ItsBreadTime/van-child-safety/test_runs/lab-validation/T-BLE-FP-ACTIVE-01/README.md

# T-BLE-FP-ACTIVE-01

Environment: simulated
Date/time: 2026-07-04T00:51:16+07:00
Firmware commit: 4d69e42
Ignition source: 
Relevant config: automated Bread iBeacon toggle while ignition_on active; verify no distress and bounded beacon chatter
Round count planned: 6
Operator: 
Supervisor: 

Physical setup:
- Door/window state:
- Fan/AC state:
- Sensor placement:
- Beacon placement:
- LD2412 target position:

Safety notes:
- Abort criteria:
- Actual abort condition reached: yes/no

Automation notes:
- MQTT log: `mqtt.log`
- Serial log: `serial.log`
- Relay snapshots: `relay_before.jsonl`, `relay_after.jsonl`
- Measurements: `measurements.csv`, `co2.csv`, `rssi.csv`
