ItsBreadTime/van-child-safety/test_runs/lab-validation/T-DISARM-02-LATENCY/README.md

# T-DISARM-02-LATENCY

Environment: simulated
Date/time: 2026-07-03T23:56:55+07:00
Firmware commit: 4d69e42
Ignition source: 
Relevant config: 10-round invalid disarm command-result latency measurement while bus is active
Round count planned: 10
Operator: 
Supervisor: 

Physical setup:
- Door/window state:
- Fan/AC state:
- Sensor placement:
- Beacon placement:
- LD2412 target position:

Safety notes:
- Abort criteria:
- Actual abort condition reached: yes/no

Automation notes:
- MQTT log: `mqtt.log`
- Serial log: `serial.log`
- Relay snapshots: `relay_before.jsonl`, `relay_after.jsonl`
- Measurements: `measurements.csv`, `co2.csv`, `rssi.csv`
