ItsBreadTime/van-child-safety/test_runs/lab-validation/T-DISARM-02/README.md

# T-DISARM-02

Environment: simulated
Date/time: 2026-07-03T23:42:01+07:00
Firmware commit: 4d69e42
Ignition source: 
Relevant config: invalid disarm without cabin-clear confirmation while bus is active
Round count planned: 3
Operator: 
Supervisor: 

Physical setup:
- Door/window state:
- Fan/AC state:
- Sensor placement:
- Beacon placement:
- LD2412 target position:

Safety notes:
- Abort criteria:
- Actual abort condition reached: yes/no

Automation notes:
- MQTT log: `mqtt.log`
- Serial log: `serial.log`
- Relay snapshots: `relay_before.jsonl`, `relay_after.jsonl`
- Measurements: `measurements.csv`, `co2.csv`, `rssi.csv`
