ItsBreadTime/van-child-safety/test_runs/lab-validation/T-HA-IGN-01/README.md

# T-HA-IGN-01

Environment: simulated-mqtt
Date/time: 2026-07-04T19:16:59+07:00
Firmware commit: 4d69e42
Ignition source: 
Relevant config: bus_empty_on/off override; observe MQTT bus/state fields consumed by HA entities
Round count planned: 1
Operator: operator
Supervisor: 

Physical setup:
- Door/window state:
- Fan/AC state:
- Sensor placement:
- Beacon placement:
- LD2412 target position:

Safety notes:
- Abort criteria:
- Actual abort condition reached: yes/no

Automation notes:
- MQTT log: `mqtt.log`
- Serial log: `serial.log`
- Relay snapshots: `relay_before.jsonl`, `relay_after.jsonl`
- Measurements: `measurements.csv`, `co2.csv`, `rssi.csv`
