ItsBreadTime/van-child-safety/test_runs/lab-validation/T-HA-ZONE-01/README.md

# T-HA-ZONE-01

Environment: simulated
Date/time: 2026-07-03T23:32:32+07:00
Firmware commit: 4d69e42
Ignition source: 
Relevant config: publish bus/ha/location/event zone_enter/zone_leave
Round count planned: 3
Operator: 
Supervisor: 

Physical setup:
- Door/window state:
- Fan/AC state:
- Sensor placement:
- Beacon placement:
- LD2412 target position:

Safety notes:
- Abort criteria:
- Actual abort condition reached: yes/no

Automation notes:
- MQTT log: `mqtt.log`
- Serial log: `serial.log`
- Relay snapshots: `relay_before.jsonl`, `relay_after.jsonl`
- Measurements: `measurements.csv`, `co2.csv`, `rssi.csv`
