ItsBreadTime/van-child-safety/test_runs/lab-validation/T-IGN-ESPNOW-01/README.md

# T-IGN-ESPNOW-01

Environment: simulated
Date/time: 2026-07-04T00:00:21+07:00
Firmware commit: 4d69e42
Ignition source: espnow
Relevant config: ESP-NOW remote unplug while active; observe ok to stale and active to exit_grace, then replug before armed distress
Round count planned: 1
Operator: 
Supervisor: 

Physical setup:
- Door/window state:
- Fan/AC state:
- Sensor placement:
- Beacon placement:
- LD2412 target position:

Safety notes:
- Abort criteria:
- Actual abort condition reached: yes/no

Automation notes:
- MQTT log: `mqtt.log`
- Serial log: `serial.log`
- Relay snapshots: `relay_before.jsonl`, `relay_after.jsonl`
- Measurements: `measurements.csv`, `co2.csv`, `rssi.csv`
