ItsBreadTime/van-child-safety/test_runs/lab-validation/T-LD-ARMENTRY-01/README.md

# T-LD-ARMENTRY-01

Environment: simulated
Date/time: 2026-07-04T13:14:01+07:00
Firmware commit: 4d69e42
Ignition source: 
Relevant config: desk proxy LD2412/mmWave armed trigger with target already present at arm time; real Discord distress allowed; fallback because passive target did not clear
Round count planned: 1
Operator: 
Supervisor: 

Physical setup:
- Door/window state:
- Fan/AC state:
- Sensor placement:
- Beacon placement:
- LD2412 target position:

Safety notes:
- Abort criteria:
- Actual abort condition reached: yes/no

Automation notes:
- MQTT log: `mqtt.log`
- Serial log: `serial.log`
- Relay snapshots: `relay_before.jsonl`, `relay_after.jsonl`
- Measurements: `measurements.csv`, `co2.csv`, `rssi.csv`
