ItsBreadTime/van-child-safety/test_runs/lab-validation/T-LD2412-PASSIVE-01/README.md

# T-LD2412-PASSIVE-01

Environment: simulated
Date/time: 2026-07-04T13:09:19+07:00
Firmware commit: 4d69e42
Ignition source: 
Relevant config: active-state LD2412/mmWave target movement observation; user moves out of and back into sensor range; no arming
Round count planned: 1
Operator: 
Supervisor: 

Physical setup:
- Door/window state:
- Fan/AC state:
- Sensor placement:
- Beacon placement:
- LD2412 target position:

Safety notes:
- Abort criteria:
- Actual abort condition reached: yes/no

Automation notes:
- MQTT log: `mqtt.log`
- Serial log: `serial.log`
- Relay snapshots: `relay_before.jsonl`, `relay_after.jsonl`
- Measurements: `measurements.csv`, `co2.csv`, `rssi.csv`
