ItsBreadTime/van-child-safety/test_runs/lab-validation/T-BLE-01/bread_beacon_test_logcat.txt

--------- beginning of system
07-04 12:09:19.528 <pid> <pid> I ActivityManager: Force stopping com.example.redacted appid=<id> user=<id>: from process=<id>
07-04 12:09:19.542 <pid> <pid> W ActivityManager: Invalid packageName: com.example.redacted
07-04 12:09:19.646 <pid> <pid> I ActivityManager: Start proc <pid>:<process> for next-top-activity {io.example.busbeacontest} caller=com.example.redacted
07-04 12:09:19.647 <pid> <pid> I ActivityManager: ProcessObserver broadcast disabled
--------- beginning of main
07-04 12:09:19.733 <pid> <pid> I BreadBeaconTest: command_activity action=io.example.busbeacontest
07-04 12:09:19.753 <pid> <pid> I ActivityManager: Background started FGS: Allowed [callingPackage: io.example.busbeacontest; callingUid=<id>; uidState: TOP ; uidBFSL: [BFSL]; intent: Intent { act=io.example.busbeacontest xflg=0x4 cmp=io.example.busbeacontest }; code:PROC_STATE_TOP; tempAllowListReason:<null>; allowWiu:12; targetSdkVersion=<version>; callerTargetSdkVersion=<version>; startForegroundCount=<count>; bindFromPackage:null: isBindService:false]
07-04 12:09:19.754 <pid> <pid> I ActivityManager: Cancel FGS notification userId=<id> definingUid=<id> packageName: io.example.busbeacontest processName:io.example.busbeacontest ChannelId:bread-beacon-test foregroundNotiWhen=<timestamp> Notiflags=<flags>
07-04 12:09:19.756 <pid> <pid> I ActivityManager: Cancel FGS notification userId=<id> definingUid=<id> packageName: io.example.busbeacontest processName:io.example.busbeacontest ChannelId:bread-beacon-test foregroundNotiWhen=<timestamp> Notiflags=<flags>
07-04 12:09:21.856 <pid> <pid> I BreadBeaconTest: command_activity action=io.example.busbeacontest
07-04 12:09:21.857 <pid> <pid> I ActivityManager: Background started FGS: Allowed [callingPackage: io.example.busbeacontest; callingUid=<id>; uidState: TOP ; uidBFSL: [BFSL]; intent: Intent { act=io.example.busbeacontest xflg=0x4 cmp=io.example.busbeacontest }; code:PROC_STATE_TOP; tempAllowListReason:<null>; allowWiu:12; targetSdkVersion=<version>; callerTargetSdkVersion=<version>; startForegroundCount=<count>; bindFromPackage:null: isBindService:false]
07-04 12:09:21.870 <pid> <pid> D BluetoothLeAdvertiser: TxPower == ADVERTISE_TX_POWER_HIGH
07-04 12:09:21.873 <pid> <pid> I BreadBeaconTest: advertise_start_requested uuid=00000000-0000-4000-8000-000000000000 major=1001 minor=2001
07-04 12:09:21.889 <pid> <pid> I BreadBeaconTest: advertise_start_success
07-04 12:09:23.995 <pid> <pid> I ActivityManager: Start proc <pid>:<process> for broadcast {com.example.redacted} caller=com.example.redacted
07-04 12:09:23.995 <pid> <pid> I ActivityManager: ProcessObserver broadcast disabled
07-04 12:09:24.772 <pid> <pid> I ActivityManager: unbindService com.example.redacted@<object> conn=android.os.BinderProxy@<object> callingPid=<id>
07-04 12:09:24.774 <pid> <pid> I ActivityManager: unbindService com.example.redacted@<object> conn=android.os.BinderProxy@<object> callingPid=<id>
07-04 12:09:24.779 <pid> <pid> I ActivityManager: unbindService com.example.redacted@<object> conn=android.os.BinderProxy@<object> callingPid=<id>
07-04 12:09:24.798 <pid> <pid> I ActivityManager: unbindService com.example.redacted@<object> conn=android.os.BinderProxy@<object> callingPid=<id>
07-04 12:09:24.815 <pid> <pid> I ActivityManager: unbindService com.example.redacted@<object> conn=android.os.BinderProxy@<object> callingPid=<id>
07-04 12:09:24.875 <pid> <pid> I ActivityManager: Killing <pid>:<process> (adj 905): normal_mem_pressure
07-04 12:09:25.165 <pid> <pid> I ActivityManager: unbindService com.example.redacted@<object> conn=android.os.BinderProxy@<object> callingPid=<id>
07-04 12:09:25.234 <pid> <pid> I ActivityManager: unbindService com.example.redacted@<object> conn=android.os.BinderProxy@<object> callingPid=<id>
07-04 12:09:25.434 <pid> <pid> I ActivityManager: Start proc <pid>:<process> for content provider {com.example.redacted} caller=com.example.redacted
07-04 12:09:25.435 <pid> <pid> I ActivityManager: ProcessObserver broadcast disabled
07-04 12:09:25.895 <pid> <pid> W ActivityManager: pid=<id> com.example.redacted sent binder code 1 with flags 2 to frozen apps and got error -74
07-04 12:09:25.903 <pid> <pid> W ActivityManager: pid=<id> com.example.redacted sent binder code 1 with flags 2 to frozen apps and got error -74
07-04 12:09:26.529 <pid> <pid> W ActivityManager: Unbind failed: could not find connection for android.os.BinderProxy@<object>
07-04 12:09:26.530 <pid> <pid> W ActivityManager: Unable to start service Intent { act=android.telephony.satellite.SatelliteService xflg=0x4 pkg=com.example.redacted } U=0: not found
07-04 12:09:32.531 <pid> <pid> I ActivityManager: unbindService com.example.redacted@<object> conn=android.os.BinderProxy@<object> callingPid=<id>
07-04 12:09:33.549 <pid> <pid> I ActivityManager: unbindService com.example.redacted@<object> conn=android.os.BinderProxy@<object> callingPid=<id>
07-04 12:09:39.002 <pid> <pid> I ActivityManager: unbindService com.example.redacted@<object> conn=android.os.BinderProxy@<object> callingPid=<id>
07-04 12:09:39.787 <pid> <pid> I ActivityManager: unbindService com.example.redacted@<object> conn=android.os.BinderProxy@<object> callingPid=<id>
07-04 12:09:39.789 <pid> <pid> I ActivityManager: unbindService com.example.redacted@<object> conn=android.os.BinderProxy@<object> callingPid=<id>
07-04 12:09:40.200 <pid> <pid> I ActivityManager: unbindService com.example.redacted@<object> conn=android.os.BinderProxy@<object> callingPid=<id>
07-04 12:09:40.207 <pid> <pid> I ActivityManager: unbindService com.example.redacted@<object> conn=android.os.BinderProxy@<object> callingPid=<id>
07-04 12:09:40.325 <pid> <pid> I ActivityManager: Start proc <pid>:<process> for service {com.example.redacted} caller=com.example.redacted
07-04 12:09:40.325 <pid> <pid> I ActivityManager: ProcessObserver broadcast disabled
07-04 12:09:41.819 <pid> <pid> I ActivityManager: unbindService com.example.redacted@<object> conn=android.app.LoadedApk$ServiceDispatcher$InnerConnection@<object> callingPid=<id> callers: com.example.redacted:5455 com.example.redacted:5328 com.example.redacted:5626 com.example.redacted:3471 android.accounts.IAccountAuthenticatorResponse$Stub.onTransact:106 android.os.Binder.execTransactInternal:1433 android.os.Binder.execTransact:1372 <bottom of call stack> <bottom of call stack> <bottom of call stack> 
07-04 12:09:43.334 <pid> <pid> I ActivityManager: unbindService com.example.redacted@<object> conn=android.app.LoadedApk$ServiceDispatcher$InnerConnection@<object> callingPid=<id> callers: com.example.redacted:5455 com.example.redacted:5328 com.example.redacted:5626 com.example.redacted:3471 android.accounts.IAccountAuthenticatorResponse$Stub.onTransact:106 android.os.Binder.execTransactInternal:1433 android.os.Binder.execTransact:1372 <bottom of call stack> <bottom of call stack> <bottom of call stack> 
07-04 12:09:44.851 <pid> <pid> I ActivityManager: unbindService com.example.redacted@<object> conn=android.app.LoadedApk$ServiceDispatcher$InnerConnection@<object> callingPid=<id> callers: com.example.redacted:5455 com.example.redacted:5328 com.example.redacted:5626 com.example.redacted:3471 android.accounts.IAccountAuthenticatorResponse$Stub.onTransact:106 android.os.Binder.execTransactInternal:1433 android.os.Binder.execTransact:1372 <bottom of call stack> <bottom of call stack> <bottom of call stack> 
07-04 12:09:46.364 <pid> <pid> I ActivityManager: unbindService com.example.redacted@<object> conn=android.app.LoadedApk$ServiceDispatcher$InnerConnection@<object> callingPid=<id> callers: com.example.redacted:5455 com.example.redacted:5328 com.example.redacted:5626 com.example.redacted:3471 android.accounts.IAccountAuthenticatorResponse$Stub.onTransact:106 android.os.Binder.execTransactInternal:1433 android.os.Binder.execTransact:1372 <bottom of call stack> <bottom of call stack> <bottom of call stack> 
07-04 12:09:46.518 <pid> <pid> I ActivityManager: Waited long enough for: ServiceRecord{5984d0c u0 com.example.redacted c:com.example.redacted}
07-04 12:09:47.876 <pid> <pid> I ActivityManager: unbindService com.example.redacted@<object> conn=android.app.LoadedApk$ServiceDispatcher$InnerConnection@<object> callingPid=<id> callers: com.example.redacted:5455 com.example.redacted:5328 com.example.redacted:5626 com.example.redacted:3471 android.accounts.IAccountAuthenticatorResponse$Stub.onTransact:106 android.os.Binder.execTransactInternal:1433 android.os.Binder.execTransact:1372 <bottom of call stack> <bottom of call stack> <bottom of call stack> 
07-04 12:09:49.022 <pid> <pid> I ActivityManager: unbindService com.example.redacted@<object> conn=android.os.BinderProxy@<object> callingPid=<id>
07-04 12:09:49.391 <pid> <pid> I ActivityManager: unbindService com.example.redacted@<object> conn=android.app.LoadedApk$ServiceDispatcher$InnerConnection@<object> callingPid=<id> callers: com.example.redacted:5455 com.example.redacted:5328 com.example.redacted:5626 com.example.redacted:3471 android.accounts.IAccountAuthenticatorResponse$Stub.onTransact:106 android.os.Binder.execTransactInternal:1433 android.os.Binder.execTransact:1372 <bottom of call stack> <bottom of call stack> <bottom of call stack> 
07-04 12:09:50.550 <pid> <pid> W ActivityManager: Unable to start service Intent { act=onetrack.action.TRACK_EVENT flg=0x2 xflg=0x4 pkg=com.example.redacted (has extras) } U=0: not found
07-04 12:09:50.906 <pid> <pid> I ActivityManager: unbindService com.example.redacted@<object> conn=android.app.LoadedApk$ServiceDispatcher$InnerConnection@<object> callingPid=<id> callers: com.example.redacted:5455 com.example.redacted:5328 com.example.redacted:5626 com.example.redacted:3471 android.accounts.IAccountAuthenticatorResponse$Stub.onTransact:106 android.os.Binder.execTransactInternal:1433 android.os.Binder.execTransact:1372 <bottom of call stack> <bottom of call stack> <bottom of call stack> 
07-04 12:09:52.421 <pid> <pid> I ActivityManager: unbindService com.example.redacted@<object> conn=android.app.LoadedApk$ServiceDispatcher$InnerConnection@<object> callingPid=<id> callers: com.example.redacted:5455 com.example.redacted:5328 com.example.redacted:5626 com.example.redacted:3471 android.accounts.IAccountAuthenticatorResponse$Stub.onTransact:106 android.os.Binder.execTransactInternal:1433 android.os.Binder.execTransact:1372 <bottom of call stack> <bottom of call stack> <bottom of call stack> 
07-04 12:09:53.937 <pid> <pid> I ActivityManager: unbindService com.example.redacted@<object> conn=android.app.LoadedApk$ServiceDispatcher$InnerConnection@<object> callingPid=<id> callers: com.example.redacted:5455 com.example.redacted:5328 com.example.redacted:5626 com.example.redacted:3471 android.accounts.IAccountAuthenticatorResponse$Stub.onTransact:106 android.os.Binder.execTransactInternal:1433 android.os.Binder.execTransact:1372 <bottom of call stack> <bottom of call stack> <bottom of call stack> 
07-04 12:09:54.707 <pid> <pid> I ActivityManager: unbindService com.example.redacted@<object> conn=android.os.BinderProxy@<object> callingPid=<id>
07-04 12:09:55.451 <pid> <pid> I ActivityManager: unbindService com.example.redacted@<object> conn=android.app.LoadedApk$ServiceDispatcher$InnerConnection@<object> callingPid=<id> callers: com.example.redacted:5455 com.example.redacted:5328 com.example.redacted:5626 com.example.redacted:3471 android.accounts.IAccountAuthenticatorResponse$Stub.onTransact:106 android.os.Binder.execTransactInternal:1433 android.os.Binder.execTransact:1372 <bottom of call stack> <bottom of call stack> <bottom of call stack> 
07-04 12:09:56.969 <pid> <pid> I ActivityManager: unbindService com.example.redacted@<object> conn=android.app.LoadedApk$ServiceDispatcher$InnerConnection@<object> callingPid=<id> callers: com.example.redacted:5455 com.example.redacted:5328 com.example.redacted:5626 com.example.redacted:3471 android.accounts.IAccountAuthenticatorResponse$Stub.onTransact:106 android.os.Binder.execTransactInternal:1433 android.os.Binder.execTransact:1372 <bottom of call stack> <bottom of call stack> <bottom of call stack> 
07-04 12:09:58.163 <pid> <pid> W ActivityManager: Unable to start service Intent { xflg=0x4 cmp=com.example.redacted } U=0: not found
07-04 12:09:58.483 <pid> <pid> I ActivityManager: unbindService com.example.redacted@<object> conn=android.app.LoadedApk$ServiceDispatcher$InnerConnection@<object> callingPid=<id> callers: com.example.redacted:5455 com.example.redacted:5328 com.example.redacted:5626 com.example.redacted:3471 android.accounts.IAccountAuthenticatorResponse$Stub.onTransact:106 android.os.Binder.execTransactInternal:1433 android.os.Binder.execTransact:1372 <bottom of call stack> <bottom of call stack> <bottom of call stack> 
07-04 12:09:59.998 <pid> <pid> I ActivityManager: unbindService com.example.redacted@<object> conn=android.app.LoadedApk$ServiceDispatcher$InnerConnection@<object> callingPid=<id> callers: com.example.redacted:5455 com.example.redacted:5328 com.example.redacted:5626 com.example.redacted:3471 android.accounts.IAccountAuthenticatorResponse$Stub.onTransact:106 android.os.Binder.execTransactInternal:1433 android.os.Binder.execTransact:1372 <bottom of call stack> <bottom of call stack> <bottom of call stack> 
07-04 12:10:00.809 <pid> <pid> W ActivityManager: Unbind failed: could not find connection for android.os.BinderProxy@<object>
07-04 12:10:00.811 <pid> <pid> W ActivityManager: Unable to start service Intent { act=android.telephony.satellite.SatelliteService xflg=0x4 pkg=com.example.redacted } U=0: not found
07-04 12:10:01.519 <pid> <pid> I ActivityManager: unbindService com.example.redacted@<object> conn=android.app.LoadedApk$ServiceDispatcher$InnerConnection@<object> callingPid=<id> callers: com.example.redacted:5455 com.example.redacted:5328 com.example.redacted:5626 com.example.redacted:3471 android.accounts.IAccountAuthenticatorResponse$Stub.onTransact:106 android.os.Binder.execTransactInternal:1433 android.os.Binder.execTransact:1372 <bottom of call stack> <bottom of call stack> <bottom of call stack> 
07-04 12:10:03.034 <pid> <pid> I ActivityManager: unbindService com.example.redacted@<object> conn=android.app.LoadedApk$ServiceDispatcher$InnerConnection@<object> callingPid=<id> callers: com.example.redacted:5455 com.example.redacted:5328 com.example.redacted:5626 com.example.redacted:3471 android.accounts.IAccountAuthenticatorResponse$Stub.onTransact:106 android.os.Binder.execTransactInternal:1433 android.os.Binder.execTransact:1372 <bottom of call stack> <bottom of call stack> <bottom of call stack> 
07-04 12:10:04.553 <pid> <pid> I ActivityManager: unbindService com.example.redacted@<object> conn=android.app.LoadedApk$ServiceDispatcher$InnerConnection@<object> callingPid=<id> callers: com.example.redacted:5455 com.example.redacted:5328 com.example.redacted:5626 com.example.redacted:3471 android.accounts.IAccountAuthenticatorResponse$Stub.onTransact:106 android.os.Binder.execTransactInternal:1433 android.os.Binder.execTransact:1372 <bottom of call stack> <bottom of call stack> <bottom of call stack> 
07-04 12:10:06.069 <pid> <pid> I ActivityManager: unbindService com.example.redacted@<object> conn=android.app.LoadedApk$ServiceDispatcher$InnerConnection@<object> callingPid=<id> callers: com.example.redacted:5455 com.example.redacted:5328 com.example.redacted:5626 com.example.redacted:3471 android.accounts.IAccountAuthenticatorResponse$Stub.onTransact:106 android.os.Binder.execTransactInternal:1433 android.os.Binder.execTransact:1372 <bottom of call stack> <bottom of call stack> <bottom of call stack> 
07-04 12:10:07.588 <pid> <pid> I ActivityManager: unbindService com.example.redacted@<object> conn=android.app.LoadedApk$ServiceDispatcher$InnerConnection@<object> callingPid=<id> callers: com.example.redacted:5455 com.example.redacted:5328 com.example.redacted:5626 com.example.redacted:3471 android.accounts.IAccountAuthenticatorResponse$Stub.onTransact:106 android.os.Binder.execTransactInternal:1433 android.os.Binder.execTransact:1372 <bottom of call stack> <bottom of call stack> <bottom of call stack> 
07-04 12:10:09.108 <pid> <pid> I ActivityManager: unbindService com.example.redacted@<object> conn=android.app.LoadedApk$ServiceDispatcher$InnerConnection@<object> callingPid=<id> callers: com.example.redacted:5455 com.example.redacted:5328 com.example.redacted:5626 com.example.redacted:3471 android.accounts.IAccountAuthenticatorResponse$Stub.onTransact:106 android.os.Binder.execTransactInternal:1433 android.os.Binder.execTransact:1372 <bottom of call stack> <bottom of call stack> <bottom of call stack> 
07-04 12:10:09.694 <pid> <pid> I ActivityManager: unbindService com.example.redacted@<object> conn=android.os.BinderProxy@<object> callingPid=<id>
07-04 12:10:10.626 <pid> <pid> I ActivityManager: unbindService com.example.redacted@<object> conn=android.app.LoadedApk$ServiceDispatcher$InnerConnection@<object> callingPid=<id> callers: com.example.redacted:5455 com.example.redacted:5328 com.example.redacted:5626 com.example.redacted:3471 android.accounts.IAccountAuthenticatorResponse$Stub.onTransact:106 android.os.Binder.execTransactInternal:1433 android.os.Binder.execTransact:1372 <bottom of call stack> <bottom of call stack> <bottom of call stack> 
07-04 12:10:12.143 <pid> <pid> I ActivityManager: unbindService com.example.redacted@<object> conn=android.app.LoadedApk$ServiceDispatcher$InnerConnection@<object> callingPid=<id> callers: com.example.redacted:5455 com.example.redacted:5328 com.example.redacted:5626 com.example.redacted:3471 android.accounts.IAccountAuthenticatorResponse$Stub.onTransact:106 android.os.Binder.execTransactInternal:1433 android.os.Binder.execTransact:1372 <bottom of call stack> <bottom of call stack> <bottom of call stack> 
07-04 12:10:13.662 <pid> <pid> I ActivityManager: unbindService com.example.redacted@<object> conn=android.app.LoadedApk$ServiceDispatcher$InnerConnection@<object> callingPid=<id> callers: com.example.redacted:5455 com.example.redacted:5328 com.example.redacted:5626 com.example.redacted:3471 android.accounts.IAccountAuthenticatorResponse$Stub.onTransact:106 android.os.Binder.execTransactInternal:1433 android.os.Binder.execTransact:1372 <bottom of call stack> <bottom of call stack> <bottom of call stack> 
07-04 12:10:15.175 <pid> <pid> I ActivityManager: unbindService com.example.redacted@<object> conn=android.app.LoadedApk$ServiceDispatcher$InnerConnection@<object> callingPid=<id> callers: com.example.redacted:5455 com.example.redacted:5328 com.example.redacted:5626 com.example.redacted:3471 android.accounts.IAccountAuthenticatorResponse$Stub.onTransact:106 android.os.Binder.execTransactInternal:1433 android.os.Binder.execTransact:1372 <bottom of call stack> <bottom of call stack> <bottom of call stack> 
07-04 12:10:16.692 <pid> <pid> I ActivityManager: unbindService com.example.redacted@<object> conn=android.app.LoadedApk$ServiceDispatcher$InnerConnection@<object> callingPid=<id> callers: com.example.redacted:5455 com.example.redacted:5328 com.example.redacted:5626 com.example.redacted:3471 android.accounts.IAccountAuthenticatorResponse$Stub.onTransact:106 android.os.Binder.execTransactInternal:1433 android.os.Binder.execTransact:1372 <bottom of call stack> <bottom of call stack> <bottom of call stack> 
07-04 12:10:18.208 <pid> <pid> I ActivityManager: unbindService com.example.redacted@<object> conn=android.app.LoadedApk$ServiceDispatcher$InnerConnection@<object> callingPid=<id> callers: com.example.redacted:5455 com.example.redacted:5328 com.example.redacted:5626 com.example.redacted:3471 android.accounts.IAccountAuthenticatorResponse$Stub.onTransact:106 android.os.Binder.execTransactInternal:1433 android.os.Binder.execTransact:1372 <bottom of call stack> <bottom of call stack> <bottom of call stack> 
07-04 12:10:19.726 <pid> <pid> I ActivityManager: unbindService com.example.redacted@<object> conn=android.app.LoadedApk$ServiceDispatcher$InnerConnection@<object> callingPid=<id> callers: com.example.redacted:5455 com.example.redacted:5328 com.example.redacted:5626 com.example.redacted:3471 android.accounts.IAccountAuthenticatorResponse$Stub.onTransact:106 android.os.Binder.execTransactInternal:1433 android.os.Binder.execTransact:1372 <bottom of call stack> <bottom of call stack> <bottom of call stack> 
07-04 12:10:21.242 <pid> <pid> I ActivityManager: unbindService com.example.redacted@<object> conn=android.app.LoadedApk$ServiceDispatcher$InnerConnection@<object> callingPid=<id> callers: com.example.redacted:5455 com.example.redacted:5328 com.example.redacted:5626 com.example.redacted:3471 android.accounts.IAccountAuthenticatorResponse$Stub.onTransact:106 android.os.Binder.execTransactInternal:1433 android.os.Binder.execTransact:1372 <bottom of call stack> <bottom of call stack> <bottom of call stack> 
07-04 12:10:22.756 <pid> <pid> I ActivityManager: unbindService com.example.redacted@<object> conn=android.app.LoadedApk$ServiceDispatcher$InnerConnection@<object> callingPid=<id> callers: com.example.redacted:5455 com.example.redacted:5328 com.example.redacted:5626 com.example.redacted:3471 android.accounts.IAccountAuthenticatorResponse$Stub.onTransact:106 android.os.Binder.execTransactInternal:1433 android.os.Binder.execTransact:1372 <bottom of call stack> <bottom of call stack> <bottom of call stack> 
07-04 12:10:24.273 <pid> <pid> I ActivityManager: unbindService com.example.redacted@<object> conn=android.app.LoadedApk$ServiceDispatcher$InnerConnection@<object> callingPid=<id> callers: com.example.redacted:5455 com.example.redacted:5328 com.example.redacted:5626 com.example.redacted:3471 android.accounts.IAccountAuthenticatorResponse$Stub.onTransact:106 android.os.Binder.execTransactInternal:1433 android.os.Binder.execTransact:1372 <bottom of call stack> <bottom of call stack> <bottom of call stack> 
07-04 12:10:25.790 <pid> <pid> I ActivityManager: unbindService com.example.redacted@<object> conn=android.app.LoadedApk$ServiceDispatcher$InnerConnection@<object> callingPid=<id> callers: com.example.redacted:5455 com.example.redacted:5328 com.example.redacted:5626 com.example.redacted:3471 android.accounts.IAccountAuthenticatorResponse$Stub.onTransact:106 android.os.Binder.execTransactInternal:1433 android.os.Binder.execTransact:1372 <bottom of call stack> <bottom of call stack> <bottom of call stack> 
07-04 12:10:27.307 <pid> <pid> I ActivityManager: unbindService com.example.redacted@<object> conn=android.app.LoadedApk$ServiceDispatcher$InnerConnection@<object> callingPid=<id> callers: com.example.redacted:5455 com.example.redacted:5328 com.example.redacted:5626 com.example.redacted:3471 android.accounts.IAccountAuthenticatorResponse$Stub.onTransact:106 android.os.Binder.execTransactInternal:1433 android.os.Binder.execTransact:1372 <bottom of call stack> <bottom of call stack> <bottom of call stack> 
07-04 12:10:28.822 <pid> <pid> I ActivityManager: unbindService com.example.redacted@<object> conn=android.app.LoadedApk$ServiceDispatcher$InnerConnection@<object> callingPid=<id> callers: com.example.redacted:5455 com.example.redacted:5328 com.example.redacted:5626 com.example.redacted:3471 android.accounts.IAccountAuthenticatorResponse$Stub.onTransact:106 android.os.Binder.execTransactInternal:1433 android.os.Binder.execTransact:1372 <bottom of call stack> <bottom of call stack> <bottom of call stack> 
07-04 12:10:30.342 <pid> <pid> I ActivityManager: unbindService com.example.redacted@<object> conn=android.app.LoadedApk$ServiceDispatcher$InnerConnection@<object> callingPid=<id> callers: com.example.redacted:5455 com.example.redacted:5328 com.example.redacted:5626 com.example.redacted:3471 android.accounts.IAccountAuthenticatorResponse$Stub.onTransact:106 android.os.Binder.execTransactInternal:1433 android.os.Binder.execTransact:1372 <bottom of call stack> <bottom of call stack> <bottom of call stack> 
07-04 12:10:31.853 <pid> <pid> I ActivityManager: unbindService com.example.redacted@<object> conn=android.app.LoadedApk$ServiceDispatcher$InnerConnection@<object> callingPid=<id> callers: com.example.redacted:5455 com.example.redacted:5328 com.example.redacted:5626 com.example.redacted:3471 android.accounts.IAccountAuthenticatorResponse$Stub.onTransact:106 android.os.Binder.execTransactInternal:1433 android.os.Binder.execTransact:1372 <bottom of call stack> <bottom of call stack> <bottom of call stack> 
07-04 12:10:33.364 <pid> <pid> I ActivityManager: unbindService com.example.redacted@<object> conn=android.app.LoadedApk$ServiceDispatcher$InnerConnection@<object> callingPid=<id> callers: com.example.redacted:5455 com.example.redacted:5328 com.example.redacted:5626 com.example.redacted:3471 android.accounts.IAccountAuthenticatorResponse$Stub.onTransact:106 android.os.Binder.execTransactInternal:1433 android.os.Binder.execTransact:1372 <bottom of call stack> <bottom of call stack> <bottom of call stack> 
07-04 12:10:34.875 <pid> <pid> I ActivityManager: unbindService com.example.redacted@<object> conn=android.app.LoadedApk$ServiceDispatcher$InnerConnection@<object> callingPid=<id> callers: com.example.redacted:5455 com.example.redacted:5328 com.example.redacted:5626 com.example.redacted:3471 android.accounts.IAccountAuthenticatorResponse$Stub.onTransact:106 android.os.Binder.execTransactInternal:1433 android.os.Binder.execTransact:1372 <bottom of call stack> <bottom of call stack> <bottom of call stack> 
07-04 12:10:36.394 <pid> <pid> I ActivityManager: unbindService com.example.redacted@<object> conn=android.app.LoadedApk$ServiceDispatcher$InnerConnection@<object> callingPid=<id> callers: com.example.redacted:5455 com.example.redacted:5328 com.example.redacted:5626 com.example.redacted:3471 android.accounts.IAccountAuthenticatorResponse$Stub.onTransact:106 android.os.Binder.execTransactInternal:1433 android.os.Binder.execTransact:1372 <bottom of call stack> <bottom of call stack> <bottom of call stack> 
07-04 12:10:37.913 <pid> <pid> I ActivityManager: unbindService com.example.redacted@<object> conn=android.app.LoadedApk$ServiceDispatcher$InnerConnection@<object> callingPid=<id> callers: com.example.redacted:5455 com.example.redacted:5328 com.example.redacted:5626 com.example.redacted:3471 android.accounts.IAccountAuthenticatorResponse$Stub.onTransact:106 android.os.Binder.execTransactInternal:1433 android.os.Binder.execTransact:1372 <bottom of call stack> <bottom of call stack> <bottom of call stack> 
07-04 12:10:39.427 <pid> <pid> I ActivityManager: unbindService com.example.redacted@<object> conn=android.app.LoadedApk$ServiceDispatcher$InnerConnection@<object> callingPid=<id> callers: com.example.redacted:5455 com.example.redacted:5328 com.example.redacted:5626 com.example.redacted:3471 android.accounts.IAccountAuthenticatorResponse$Stub.onTransact:106 android.os.Binder.execTransactInternal:1433 android.os.Binder.execTransact:1372 <bottom of call stack> <bottom of call stack> <bottom of call stack> 
07-04 12:10:40.942 <pid> <pid> I ActivityManager: unbindService com.example.redacted@<object> conn=android.app.LoadedApk$ServiceDispatcher$InnerConnection@<object> callingPid=<id> callers: com.example.redacted:5455 com.example.redacted:5328 com.example.redacted:5626 com.example.redacted:3471 android.accounts.IAccountAuthenticatorResponse$Stub.onTransact:106 android.os.Binder.execTransactInternal:1433 android.os.Binder.execTransact:1372 <bottom of call stack> <bottom of call stack> <bottom of call stack> 
07-04 12:10:42.461 <pid> <pid> I ActivityManager: unbindService com.example.redacted@<object> conn=android.app.LoadedApk$ServiceDispatcher$InnerConnection@<object> callingPid=<id> callers: com.example.redacted:5455 com.example.redacted:5328 com.example.redacted:5626 com.example.redacted:3471 android.accounts.IAccountAuthenticatorResponse$Stub.onTransact:106 android.os.Binder.execTransactInternal:1433 android.os.Binder.execTransact:1372 <bottom of call stack> <bottom of call stack> <bottom of call stack> 
07-04 12:10:43.974 <pid> <pid> I ActivityManager: unbindService com.example.redacted@<object> conn=android.app.LoadedApk$ServiceDispatcher$InnerConnection@<object> callingPid=<id> callers: com.example.redacted:5455 com.example.redacted:5328 com.example.redacted:5626 com.example.redacted:3471 android.accounts.IAccountAuthenticatorResponse$Stub.onTransact:106 android.os.Binder.execTransactInternal:1433 android.os.Binder.execTransact:1372 <bottom of call stack> <bottom of call stack> <bottom of call stack> 
07-04 12:10:44.374 <pid> <pid> W ActivityManager: Unbind failed: could not find connection for android.os.BinderProxy@<object>
07-04 12:10:44.376 <pid> <pid> W ActivityManager: Unable to start service Intent { act=android.telephony.satellite.SatelliteService xflg=0x4 pkg=com.example.redacted } U=0: not found
07-04 12:10:45.489 <pid> <pid> I ActivityManager: unbindService com.example.redacted@<object> conn=android.app.LoadedApk$ServiceDispatcher$InnerConnection@<object> callingPid=<id> callers: com.example.redacted:5455 com.example.redacted:5328 com.example.redacted:5626 com.example.redacted:3471 android.accounts.IAccountAuthenticatorResponse$Stub.onTransact:106 android.os.Binder.execTransactInternal:1433 android.os.Binder.execTransact:1372 <bottom of call stack> <bottom of call stack> <bottom of call stack> 
07-04 12:10:47.005 <pid> <pid> I ActivityManager: unbindService com.example.redacted@<object> conn=android.app.LoadedApk$ServiceDispatcher$InnerConnection@<object> callingPid=<id> callers: com.example.redacted:5455 com.example.redacted:5328 com.example.redacted:5626 com.example.redacted:3471 android.accounts.IAccountAuthenticatorResponse$Stub.onTransact:106 android.os.Binder.execTransactInternal:1433 android.os.Binder.execTransact:1372 <bottom of call stack> <bottom of call stack> <bottom of call stack> 
07-04 12:10:48.520 <pid> <pid> I ActivityManager: unbindService com.example.redacted@<object> conn=android.app.LoadedApk$ServiceDispatcher$InnerConnection@<object> callingPid=<id> callers: com.example.redacted:5455 com.example.redacted:5328 com.example.redacted:5626 com.example.redacted:3471 android.accounts.IAccountAuthenticatorResponse$Stub.onTransact:106 android.os.Binder.execTransactInternal:1433 android.os.Binder.execTransact:1372 <bottom of call stack> <bottom of call stack> <bottom of call stack> 
07-04 12:10:50.035 <pid> <pid> I ActivityManager: unbindService com.example.redacted@<object> conn=android.app.LoadedApk$ServiceDispatcher$InnerConnection@<object> callingPid=<id> callers: com.example.redacted:5455 com.example.redacted:5328 com.example.redacted:5626 com.example.redacted:3471 android.accounts.IAccountAuthenticatorResponse$Stub.onTransact:106 android.os.Binder.execTransactInternal:1433 android.os.Binder.execTransact:1372 <bottom of call stack> <bottom of call stack> <bottom of call stack> 
07-04 12:10:51.550 <pid> <pid> I ActivityManager: unbindService com.example.redacted@<object> conn=android.app.LoadedApk$ServiceDispatcher$InnerConnection@<object> callingPid=<id> callers: com.example.redacted:5455 com.example.redacted:5328 com.example.redacted:5626 com.example.redacted:3471 android.accounts.IAccountAuthenticatorResponse$Stub.onTransact:106 android.os.Binder.execTransactInternal:1433 android.os.Binder.execTransact:1372 <bottom of call stack> <bottom of call stack> <bottom of call stack> 
07-04 12:10:53.067 <pid> <pid> I ActivityManager: unbindService com.example.redacted@<object> conn=android.app.LoadedApk$ServiceDispatcher$InnerConnection@<object> callingPid=<id> callers: com.example.redacted:5455 com.example.redacted:5328 com.example.redacted:5626 com.example.redacted:3471 android.accounts.IAccountAuthenticatorResponse$Stub.onTransact:106 android.os.Binder.execTransactInternal:1433 android.os.Binder.execTransact:1372 <bottom of call stack> <bottom of call stack> <bottom of call stack> 
07-04 12:10:54.582 <pid> <pid> I ActivityManager: unbindService com.example.redacted@<object> conn=android.app.LoadedApk$ServiceDispatcher$InnerConnection@<object> callingPid=<id> callers: com.example.redacted:5455 com.example.redacted:5328 com.example.redacted:5626 com.example.redacted:3471 android.accounts.IAccountAuthenticatorResponse$Stub.onTransact:106 android.os.Binder.execTransactInternal:1433 android.os.Binder.execTransact:1372 <bottom of call stack> <bottom of call stack> <bottom of call stack> 
07-04 12:10:56.103 <pid> <pid> I ActivityManager: unbindService com.example.redacted@<object> conn=android.app.LoadedApk$ServiceDispatcher$InnerConnection@<object> callingPid=<id> callers: com.example.redacted:5455 com.example.redacted:5328 com.example.redacted:5626 com.example.redacted:3471 android.accounts.IAccountAuthenticatorResponse$Stub.onTransact:106 android.os.Binder.execTransactInternal:1433 android.os.Binder.execTransact:1372 <bottom of call stack> <bottom of call stack> <bottom of call stack> 
07-04 12:10:57.617 <pid> <pid> I ActivityManager: unbindService com.example.redacted@<object> conn=android.app.LoadedApk$ServiceDispatcher$InnerConnection@<object> callingPid=<id> callers: com.example.redacted:5455 com.example.redacted:5328 com.example.redacted:5626 com.example.redacted:3471 android.accounts.IAccountAuthenticatorResponse$Stub.onTransact:106 android.os.Binder.execTransactInternal:1433 android.os.Binder.execTransact:1372 <bottom of call stack> <bottom of call stack> <bottom of call stack> 
07-04 12:10:58.201 <pid> <pid> W ActivityManager: Unable to start service Intent { xflg=0x4 cmp=com.example.redacted } U=0: not found
07-04 12:10:59.130 <pid> <pid> I ActivityManager: unbindService com.example.redacted@<object> conn=android.app.LoadedApk$ServiceDispatcher$InnerConnection@<object> callingPid=<id> callers: com.example.redacted:5455 com.example.redacted:5328 com.example.redacted:5626 com.example.redacted:3471 android.accounts.IAccountAuthenticatorResponse$Stub.onTransact:106 android.os.Binder.execTransactInternal:1433 android.os.Binder.execTransact:1372 <bottom of call stack> <bottom of call stack> <bottom of call stack> 
07-04 12:11:00.643 <pid> <pid> I ActivityManager: unbindService com.example.redacted@<object> conn=android.app.LoadedApk$ServiceDispatcher$InnerConnection@<object> callingPid=<id> callers: com.example.redacted:5455 com.example.redacted:5328 com.example.redacted:5626 com.example.redacted:3471 android.accounts.IAccountAuthenticatorResponse$Stub.onTransact:106 android.os.Binder.execTransactInternal:1433 android.os.Binder.execTransact:1372 <bottom of call stack> <bottom of call stack> <bottom of call stack> 
07-04 12:11:02.159 <pid> <pid> I ActivityManager: unbindService com.example.redacted@<object> conn=android.app.LoadedApk$ServiceDispatcher$InnerConnection@<object> callingPid=<id> callers: com.example.redacted:5455 com.example.redacted:5328 com.example.redacted:5626 com.example.redacted:3471 android.accounts.IAccountAuthenticatorResponse$Stub.onTransact:106 android.os.Binder.execTransactInternal:1433 android.os.Binder.execTransact:1372 <bottom of call stack> <bottom of call stack> <bottom of call stack> 
07-04 12:11:03.678 <pid> <pid> I ActivityManager: unbindService com.example.redacted@<object> conn=android.app.LoadedApk$ServiceDispatcher$InnerConnection@<object> callingPid=<id> callers: com.example.redacted:5455 com.example.redacted:5328 com.example.redacted:5626 com.example.redacted:3471 android.accounts.IAccountAuthenticatorResponse$Stub.onTransact:106 android.os.Binder.execTransactInternal:1433 android.os.Binder.execTransact:1372 <bottom of call stack> <bottom of call stack> <bottom of call stack> 
07-04 12:11:05.194 <pid> <pid> I ActivityManager: unbindService com.example.redacted@<object> conn=android.app.LoadedApk$ServiceDispatcher$InnerConnection@<object> callingPid=<id> callers: com.example.redacted:5455 com.example.redacted:5328 com.example.redacted:5626 com.example.redacted:3471 android.accounts.IAccountAuthenticatorResponse$Stub.onTransact:106 android.os.Binder.execTransactInternal:1433 android.os.Binder.execTransact:1372 <bottom of call stack> <bottom of call stack> <bottom of call stack> 
07-04 12:11:06.713 <pid> <pid> I ActivityManager: unbindService com.example.redacted@<object> conn=android.app.LoadedApk$ServiceDispatcher$InnerConnection@<object> callingPid=<id> callers: com.example.redacted:5455 com.example.redacted:5328 com.example.redacted:5626 com.example.redacted:3471 android.accounts.IAccountAuthenticatorResponse$Stub.onTransact:106 android.os.Binder.execTransactInternal:1433 android.os.Binder.execTransact:1372 <bottom of call stack> <bottom of call stack> <bottom of call stack> 
07-04 12:11:08.229 <pid> <pid> I ActivityManager: unbindService com.example.redacted@<object> conn=android.app.LoadedApk$ServiceDispatcher$InnerConnection@<object> callingPid=<id> callers: com.example.redacted:5455 com.example.redacted:5328 com.example.redacted:5626 com.example.redacted:3471 android.accounts.IAccountAuthenticatorResponse$Stub.onTransact:106 android.os.Binder.execTransactInternal:1433 android.os.Binder.execTransact:1372 <bottom of call stack> <bottom of call stack> <bottom of call stack> 
07-04 12:11:09.751 <pid> <pid> I ActivityManager: unbindService com.example.redacted@<object> conn=android.app.LoadedApk$ServiceDispatcher$InnerConnection@<object> callingPid=<id> callers: com.example.redacted:5455 com.example.redacted:5328 com.example.redacted:5626 com.example.redacted:3471 android.accounts.IAccountAuthenticatorResponse$Stub.onTransact:106 android.os.Binder.execTransactInternal:1433 android.os.Binder.execTransact:1372 <bottom of call stack> <bottom of call stack> <bottom of call stack> 
07-04 12:11:11.265 <pid> <pid> I ActivityManager: unbindService com.example.redacted@<object> conn=android.app.LoadedApk$ServiceDispatcher$InnerConnection@<object> callingPid=<id> callers: com.example.redacted:5455 com.example.redacted:5328 com.example.redacted:5626 com.example.redacted:3471 android.accounts.IAccountAuthenticatorResponse$Stub.onTransact:106 android.os.Binder.execTransactInternal:1433 android.os.Binder.execTransact:1372 <bottom of call stack> <bottom of call stack> <bottom of call stack> 
07-04 12:11:12.785 <pid> <pid> I ActivityManager: unbindService com.example.redacted@<object> conn=android.app.LoadedApk$ServiceDispatcher$InnerConnection@<object> callingPid=<id> callers: com.example.redacted:5455 com.example.redacted:5328 com.example.redacted:5626 com.example.redacted:3471 android.accounts.IAccountAuthenticatorResponse$Stub.onTransact:106 android.os.Binder.execTransactInternal:1433 android.os.Binder.execTransact:1372 <bottom of call stack> <bottom of call stack> <bottom of call stack> 
07-04 12:11:14.300 <pid> <pid> I ActivityManager: unbindService com.example.redacted@<object> conn=android.app.LoadedApk$ServiceDispatcher$InnerConnection@<object> callingPid=<id> callers: com.example.redacted:5455 com.example.redacted:5328 com.example.redacted:5626 com.example.redacted:3471 android.accounts.IAccountAuthenticatorResponse$Stub.onTransact:106 android.os.Binder.execTransactInternal:1433 android.os.Binder.execTransact:1372 <bottom of call stack> <bottom of call stack> <bottom of call stack> 
07-04 12:11:15.821 <pid> <pid> I ActivityManager: unbindService com.example.redacted@<object> conn=android.app.LoadedApk$ServiceDispatcher$InnerConnection@<object> callingPid=<id> callers: com.example.redacted:5455 com.example.redacted:5328 com.example.redacted:5626 com.example.redacted:3471 android.accounts.IAccountAuthenticatorResponse$Stub.onTransact:106 android.os.Binder.execTransactInternal:1433 android.os.Binder.execTransact:1372 <bottom of call stack> <bottom of call stack> <bottom of call stack> 
07-04 12:11:17.339 <pid> <pid> I ActivityManager: unbindService com.example.redacted@<object> conn=android.app.LoadedApk$ServiceDispatcher$InnerConnection@<object> callingPid=<id> callers: com.example.redacted:5455 com.example.redacted:5328 com.example.redacted:5626 com.example.redacted:3471 android.accounts.IAccountAuthenticatorResponse$Stub.onTransact:106 android.os.Binder.execTransactInternal:1433 android.os.Binder.execTransact:1372 <bottom of call stack> <bottom of call stack> <bottom of call stack> 
07-04 12:11:18.852 <pid> <pid> I ActivityManager: unbindService com.example.redacted@<object> conn=android.app.LoadedApk$ServiceDispatcher$InnerConnection@<object> callingPid=<id> callers: com.example.redacted:5455 com.example.redacted:5328 com.example.redacted:5626 com.example.redacted:3471 android.accounts.IAccountAuthenticatorResponse$Stub.onTransact:106 android.os.Binder.execTransactInternal:1433 android.os.Binder.execTransact:1372 <bottom of call stack> <bottom of call stack> <bottom of call stack> 
07-04 12:11:20.370 <pid> <pid> I ActivityManager: unbindService com.example.redacted@<object> conn=android.app.LoadedApk$ServiceDispatcher$InnerConnection@<object> callingPid=<id> callers: com.example.redacted:5455 com.example.redacted:5328 com.example.redacted:5626 com.example.redacted:3471 android.accounts.IAccountAuthenticatorResponse$Stub.onTransact:106 android.os.Binder.execTransactInternal:1433 android.os.Binder.execTransact:1372 <bottom of call stack> <bottom of call stack> <bottom of call stack> 
07-04 12:11:21.883 <pid> <pid> I ActivityManager: unbindService com.example.redacted@<object> conn=android.app.LoadedApk$ServiceDispatcher$InnerConnection@<object> callingPid=<id> callers: com.example.redacted:5455 com.example.redacted:5328 com.example.redacted:5626 com.example.redacted:3471 android.accounts.IAccountAuthenticatorResponse$Stub.onTransact:106 android.os.Binder.execTransactInternal:1433 android.os.Binder.execTransact:1372 <bottom of call stack> <bottom of call stack> <bottom of call stack> 
07-04 12:11:23.396 <pid> <pid> I ActivityManager: unbindService com.example.redacted@<object> conn=android.app.LoadedApk$ServiceDispatcher$InnerConnection@<object> callingPid=<id> callers: com.example.redacted:5455 com.example.redacted:5328 com.example.redacted:5626 com.example.redacted:3471 android.accounts.IAccountAuthenticatorResponse$Stub.onTransact:106 android.os.Binder.execTransactInternal:1433 android.os.Binder.execTransact:1372 <bottom of call stack> <bottom of call stack> <bottom of call stack> 
07-04 12:11:23.790 <pid> <pid> W ActivityManager: Unbind failed: could not find connection for android.os.BinderProxy@<object>
07-04 12:11:23.792 <pid> <pid> W ActivityManager: Unable to start service Intent { act=android.telephony.satellite.SatelliteService xflg=0x4 pkg=com.example.redacted } U=0: not found
07-04 12:11:24.683 <pid> <pid> I ActivityManager: Start proc <pid>:<process> for broadcast {com.example.redacted} caller=com.example.redacted
07-04 12:11:24.683 <pid> <pid> I ActivityManager: ProcessObserver broadcast disabled
07-04 12:11:24.908 <pid> <pid> I ActivityManager: unbindService com.example.redacted@<object> conn=android.app.LoadedApk$ServiceDispatcher$InnerConnection@<object> callingPid=<id> callers: com.example.redacted:5455 com.example.redacted:5328 com.example.redacted:5626 com.example.redacted:3471 android.accounts.IAccountAuthenticatorResponse$Stub.onTransact:106 android.os.Binder.execTransactInternal:1433 android.os.Binder.execTransact:1372 <bottom of call stack> <bottom of call stack> <bottom of call stack> 
07-04 12:11:25.014 <pid> <pid> I ActivityManager: Start proc <pid>:<process> for  {com.example.redacted:0} caller=com.example.redacted
07-04 12:11:25.014 <pid> <pid> I ActivityManager: ProcessObserver broadcast disabled
07-04 12:11:25.092 <pid> <pid> I ActivityManager: unbindService com.example.redacted@<object> conn=android.os.BinderProxy@<object> callingPid=<id>
07-04 12:11:25.154 <pid> <pid> I ActivityManager: unbindService com.example.redacted@<object> conn=android.app.LoadedApk$ServiceDispatcher$InnerConnection@<object> callingPid=<id> callers: com.example.redacted:5455 com.example.redacted:5328 com.example.redacted:4690 com.example.redacted:4651 com.example.redacted:4686 android.accounts.IAccountAuthenticatorResponse$Stub.onTransact:106 android.os.Binder.execTransactInternal:1433 android.os.Binder.execTransact:1372 <bottom of call stack> <bottom of call stack> 
07-04 12:11:25.156 <pid> <pid> I ActivityManager: unbindService com.example.redacted@<object> conn=android.app.LoadedApk$ServiceDispatcher$InnerConnection@<object> callingPid=<id> callers: com.example.redacted:1412 com.example.redacted:1288 com.example.redacted:848 com.example.redacted:315 android.app.job.IJobCallback$Stub.onTransact:313 android.os.Binder.execTransactInternal:1428 android.os.Binder.execTransact:1372 <bottom of call stack> <bottom of call stack> <bottom of call stack> 
07-04 12:11:25.167 <pid> <pid> I ActivityManager: unbindService com.example.redacted@<object> conn=android.app.LoadedApk$ServiceDispatcher$InnerConnection@<object> callingPid=<id> callers: com.example.redacted:1412 com.example.redacted:1288 com.example.redacted:1269 com.example.redacted:912 com.example.redacted:300 android.app.job.IJobCallback$Stub.onTransact:280 android.os.Binder.execTransactInternal:1433 android.os.Binder.execTransact:1372 <bottom of call stack> <bottom of call stack> 
07-04 12:11:25.188 <pid> <pid> I ActivityManager: unbindService com.example.redacted@<object> conn=android.app.LoadedApk$ServiceDispatcher$InnerConnection@<object> callingPid=<id> callers: com.example.redacted:1412 com.example.redacted:1288 com.example.redacted:848 com.example.redacted:315 android.app.job.IJobCallback$Stub.onTransact:313 android.os.Binder.execTransactInternal:1428 android.os.Binder.execTransact:1372 <bottom of call stack> <bottom of call stack> <bottom of call stack> 
07-04 12:11:25.221 <pid> <pid> I ActivityManager: unbindService com.example.redacted@<object> conn=android.app.LoadedApk$ServiceDispatcher$InnerConnection@<object> callingPid=<id> callers: com.example.redacted:1412 com.example.redacted:1288 com.example.redacted:848 com.example.redacted:315 android.app.job.IJobCallback$Stub.onTransact:313 android.os.Binder.execTransactInternal:1433 android.os.Binder.execTransact:1372 <bottom of call stack> <bottom of call stack> <bottom of call stack> 
07-04 12:11:25.243 <pid> <pid> I BreadBeaconTest: command_activity action=io.example.busbeacontest
07-04 12:11:25.254 <pid> <pid> I BreadBeaconTest: advertise_stop_requested
07-04 12:11:25.254 <pid> <pid> I ActivityManager: Cancel FGS notification userId=<id> definingUid=<id> packageName: io.example.busbeacontest processName:io.example.busbeacontest ChannelId:bread-beacon-test foregroundNotiWhen=<timestamp> Notiflags=<flags>
07-04 12:11:25.571 <pid> <pid> I ActivityManager: unbindService com.example.redacted@<object> conn=android.app.LoadedApk$ServiceDispatcher$InnerConnection@<object> callingPid=<id> callers: com.example.redacted:1412 com.example.redacted:1288 com.example.redacted:1269 com.example.redacted:912 com.example.redacted:300 android.app.job.IJobCallback$Stub.onTransact:280 android.os.Binder.execTransactInternal:1428 android.os.Binder.execTransact:1372 <bottom of call stack> <bottom of call stack> 
07-04 12:11:25.981 <pid> <pid> I ActivityManager: unbindService com.example.redacted@<object> conn=android.os.BinderProxy@<object> callingPid=<id>
07-04 12:11:25.991 <pid> <pid> I ActivityManager: unbindService com.example.redacted@<object> conn=android.os.BinderProxy@<object> callingPid=<id>
