ItsBreadTime/van-child-safety/test_runs/lab-validation/T-HA-01/result.md

# T-HA-01 Result

Rounds passed/total: 1/1
Result: pass

Expected behavior:
The Home Assistant package, blueprint, and dashboard YAML should parse and
contain the expected entities, helper scripts, guarded disarm wiring,
distress-detail templates, relay-status availability handling, zone-event
publishing, and current dashboard action syntax.

Observed behavior:
The focused automated Home Assistant package/dashboard audit passed:
`discord_relay/tests/test_ha_package.py` ran 14 tests and all passed. The tests
validated package top-level keys, person/beacon helpers, add/update/remove/list
scripts, acknowledge/clear/test/disarm scripts, guarded disarm confirmation and
command-result wait behavior, relay status availability template, mobile push
distress filtering, empty retained distress handling, exit-grace reminders,
stale firmware alert source, school zone automations, zone blueprint parsing,
dashboard action syntax, custom-card dependency documentation, and robust
distress template access.

Metrics:
- End-to-end latency:
- Relay-only latency:
- FP count:
- FN count:
- Reconnect time:
  - Static audit tests: 14/14 passed.

Evidence files:
- relay_before.jsonl
- ha_package_pytest.txt

Notes for Chapter 4:
T-HA-01 passed 1/1 automated static audit round. This supports the Home
Assistant package/dashboard configuration structure, not a live browser
screenshot or deployed Home Assistant runtime state.

Notes for Chapter 5:
The remaining useful dashboard evidence is visual/runtime confirmation in Home
Assistant with screenshots once the deployed dashboard is open.
