ItsBreadTime/van-child-safety/test_runs/lab-validation/T-IGN-ESPNOW-03/README.md

# T-IGN-ESPNOW-03

ESP-NOW remote heartbeat timeout and recovery.
