ItsBreadTime/van-child-safety/test_runs/lab-validation/T-BLE-FP-ACTIVE-01/ble_fp_transitions.csv

step | cycle | action | target_state | command_start_iso | command_end_iso | adb_duration_ms | mqtt_iso | latency_ms | bus_state_after | armed_after | distress_active_after | distress_messages_after_command | result | mqtt_payload
1 | 1 | start | near | 2026-07-04T00:58:21.759+07:00 | 2026-07-04T00:58:21.883+07:00 | 124.0 | 2026-07-04T00:58:24.985+07:00 | 3225.9 | active | False | False | 0 | pass | {"id":"bread","name":"bread","state":"near","rssi":-59,"timestamp":"2026-07-03T17:58:25Z","person_name":"Bread","rssi_threshold":-75,"active":true,"discord_channel_id":"000000000000000000","home_zone_entity":"zone.example_home","last_seen_age_s":0}
2 | 1 | stop | absent | 2026-07-04T00:58:26.991+07:00 | 2026-07-04T00:58:27.162+07:00 | 170.7 | 2026-07-04T00:58:37.785+07:00 | 10793.3 | active | False | False | 0 | pass | {"id":"bread","name":"bread","state":"absent","rssi":0,"timestamp":"2026-07-03T17:58:37Z","person_name":"Bread","rssi_threshold":-75,"active":true,"discord_channel_id":"000000000000000000","home_zone_entity":"zone.example_home","last_seen_age_s":10}
3 | 2 | start | near | 2026-07-04T00:58:39.790+07:00 | 2026-07-04T00:58:39.922+07:00 | 132.5 | 2026-07-04T00:58:45.977+07:00 | 6186.8 | active | False | False | 0 | pass | {"id":"bread","name":"bread","state":"near","rssi":-57,"timestamp":"2026-07-03T17:58:46Z","person_name":"Bread","rssi_threshold":-75,"active":true,"discord_channel_id":"000000000000000000","home_zone_entity":"zone.example_home","last_seen_age_s":0}
4 | 2 | stop | absent | 2026-07-04T00:58:47.983+07:00 | 2026-07-04T00:58:48.132+07:00 | 148.4 | 2026-07-04T00:58:58.060+07:00 | 10077.1 | active | False | False | 0 | pass | {"id":"bread","name":"bread","state":"absent","rssi":0,"timestamp":"2026-07-03T17:58:58Z","person_name":"Bread","rssi_threshold":-75,"active":true,"discord_channel_id":"000000000000000000","home_zone_entity":"zone.example_home","last_seen_age_s":10}
5 | 3 | start | near | 2026-07-04T00:59:00.069+07:00 | 2026-07-04T00:59:00.194+07:00 | 125.3 | 2026-07-04T00:59:02.770+07:00 | 2701.5 | active | False | False | 0 | pass | {"id":"bread","name":"bread","state":"near","rssi":-66,"timestamp":"2026-07-03T17:59:02Z","person_name":"Bread","rssi_threshold":-75,"active":true,"discord_channel_id":"000000000000000000","home_zone_entity":"zone.example_home","last_seen_age_s":0}
6 | 3 | stop | absent | 2026-07-04T00:59:04.777+07:00 | 2026-07-04T00:59:04.944+07:00 | 166.9 | 2026-07-04T00:59:18.335+07:00 | 13557.8 | active | False | False | 0 | pass | {"id":"bread","name":"bread","state":"absent","rssi":0,"timestamp":"2026-07-03T17:59:18Z","person_name":"Bread","rssi_threshold":-75,"active":true,"discord_channel_id":"000000000000000000","home_zone_entity":"zone.example_home","last_seen_age_s":13}
