ItsBreadTime/van-child-safety/test_runs/lab-validation/T-IGN-RAPID-01/co2.csv

timestamp | topic | bus_state | co2 | co2_baseline | co2_delta_since_armed | co2_delta_3min | ld2412_target | gps_valid | wifi_rssi
2026-07-04T00:03:51+0700 | bus/telemetry | active | 1062 | 0 | 1062 | 9 | True | False | -57
