ItsBreadTime/van-child-safety/test_runs/lab-validation/T-MQTT-SOAK-02/telemetry_intervals.csv

index | interval_ms
1 | 30000.0
2 | 30000.0
3 | 30000.0
4 | 30000.0
5 | 30000.0
6 | 30000.0
7 | 30000.0
8 | 30000.0
9 | 30000.0
10 | 30000.0
11 | 30000.0
12 | 30000.0
13 | 30000.0
14 | 30000.0
15 | 30000.0
16 | 30000.0
17 | 30000.0
18 | 30000.0
19 | 30000.0
20 | 30000.0
21 | 30000.0
22 | 30000.0
23 | 30000.0
24 | 30000.0
25 | 30000.0
26 | 30000.0
27 | 30000.0
28 | 30000.0
29 | 30000.0
