ItsBreadTime/van-child-safety/main/i2c_bus.c

#include "driver/i2c.h"
#include "esp_log.h"
#include "i2c_bus.h"

static const char *TAG = "I2C";

void i2c_bus_init(void)
{
    i2c_config_t conf = {
        .mode = I2C_MODE_MASTER,
        .sda_io_num = 5,
        .scl_io_num = 6,
        .sda_pullup_en = GPIO_PULLUP_ENABLE,
        .scl_pullup_en = GPIO_PULLUP_ENABLE,
        .master.clk_speed = 100000,
    };

    ESP_ERROR_CHECK(i2c_param_config(I2C_NUM_0, &conf));
    ESP_ERROR_CHECK(i2c_driver_install(I2C_NUM_0, conf.mode, 0, 0, 0));
    ESP_LOGI(TAG, "I2C init (SDA=5, SCL=6)");
}
