ItsBreadTime/van-child-safety/test_runs/field-validation/T-REAL-VAN-OCCUPANT-01/config_snapshot.txt

CONFIG_SOC_WIFI_SUPPORT_VARIABLE_BEACON_WINDOW=y
CONFIG_DISTRESS_INITIAL_DELAY_S=120
CONFIG_DISTRESS_REPEAT_INTERVAL_S=60
CONFIG_PRESENCE_SUSTAIN_S=5
CONFIG_PRESENCE_SUSTAIN_ARMED_EXISTING_S=12
CONFIG_PRESENCE_TARGET_DROP_DEBOUNCE_MS=1000
CONFIG_PRESENCE_STILL_DISTANCE_MAX_CM=200
CONFIG_PRESENCE_STILL_ENERGY_MIN=0
CONFIG_IGNITION_SOURCE_ESPNOW=y
# CONFIG_IGNITION_SOURCE_GPIO is not set
CONFIG_EXIT_GRACE_SECONDS=120
CONFIG_ESPNOW_SECRET="<redacted>"
CONFIG_ESPNOW_HEARTBEAT_INTERVAL_MS=2000
CONFIG_ESPNOW_HEARTBEAT_TIMEOUT_MS=10000
CONFIG_ESPNOW_BOOT_GRACE_S=30
CONFIG_BLE_BEACON_NEAR_SUSTAIN_S=2
CONFIG_BLE_BEACON_ABSENT_TIMEOUT_S=10
CONFIG_BLE_BEACON_FAR_HYSTERESIS_DB=10
CONFIG_BLE_BEACON_MIN_NEAR_RSSI=-70
# CO2 Tracking
CONFIG_CO2_RISE_THRESHOLD_PPM=100
CONFIG_CO2_WINDOW_READINGS=7
CONFIG_CO2_REQUIRE_DELTA_3MIN_RISING=y
# end of CO2 Tracking
CONFIG_ESP_WIFI_ESPNOW_MAX_ENCRYPT_NUM=7
