ItsBreadTime/van-child-safety/main/util.h

#pragma once

#include <stdint.h>

static inline uint8_t crc8_sensirion(const uint8_t *data, int len)
{
    uint8_t crc = 0xFF;
    for (int i = 0; i < len; i++) {
        crc ^= data[i];
        for (int j = 0; j < 8; j++) {
            if (crc & 0x80)
                crc = (crc << 1) ^ 0x31;
            else
                crc <<= 1;
        }
    }
    return crc;
}
